evandrosouza-developer/ps2tomsxUSB/Documentation/Kicad/F4/PS2-MSX-F4 Back view.png

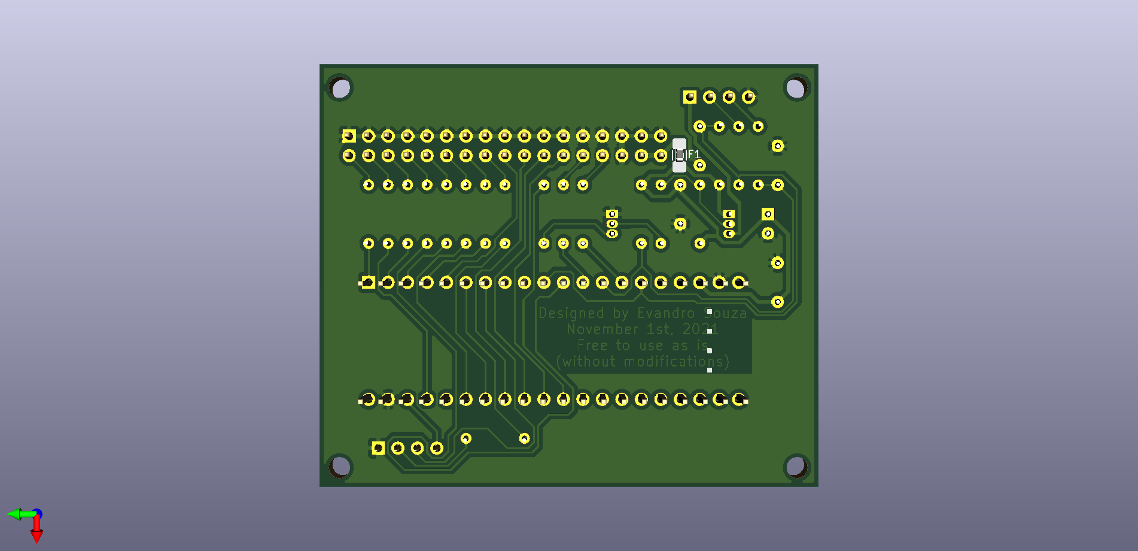
Documentation/Kicad/F4/PS2-MSX-F4 Back view.png
