evandrosouza-developer/ps2tomsxUSB/database.c

/** @addtogroup 05 dbasemgt Database Management
 *
 * @file database.c Database definition file input.
 *
 * @brief <b>Database definition, check and maintenance routines.</b>
 *
 * @version 1.0.0
 *
 * @author @htmlonly &copy; @endhtmlonly 2022
 * Evandro Souza <evandro.r.souza@gmail.com>
 *
 * @date 25 September 2022
 *
 * This library executes functions to interface and control a PS/2 keyboard, like:
 * power control of a PS/2 key, general interface to read events and write commands to PS/2
 * keyboard, including interrupt service routines on the STM32F4 and STM32F1 series of ARM
 * Cortex Microcontrollers by ST Microelectronics.
 *
 * LGPL License Terms ref lgpl_license
 */

/*
 * This file is part of the PS/2 to MSX Keyboard converter enviroment:
 * PS/2 to MSX keyboard Converter and MSX Keyboard Subsystem Emulator
 * designs, based on libopencm3 project.
 *
 * Copyright (C) 2022 Evandro Souza <evandro.r.souza@gmail.com>
 *
 * This original SW is compiled to a Sharp/Epcom MSX HB-8000 and a brazilian ABNT2 PS/2 keyboard (ID=275)
 * But it is possible to update the table sending a Intel Hex File through serial or USB
 *
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
 * You should have received a copy of the GNU Lesser General Public License
 * along with this library.  If not, see <http://www.gnu.org/licenses/>.
 */

//Use Tab width=2



const uint8_t 
#if MCU == STM32F103
__attribute__((section("MSXDATABASE"))) 
#endif  //#if MCU == STM32F103
DEFAULT_MSX_KEYB_DATABASE_CONVERSION[(uint16_t)N_DATABASE_REGISTERS][(uint8_t)DB_NUM_COLS] =
//Paste here the generated excel Conversion Database to make it as a default.
//Colar aqui Base de Dados de conversao gerada pelo excel para compilar como uma tabela default.
{
    {1, 0, 255, 255, 255, 255, 255, 255},
    {1, 0, 0, 244, 96, 112, 255, 255},
    {3, 0, 0, 244, 113, 255, 255, 255},
    {4, 0, 0, 244, 103, 255, 255, 255},
    {5, 0, 0, 244, 101, 255, 255, 255},
    {6, 0, 0, 244, 102, 255, 255, 255},
    {7, 0, 0, 244, 116, 255, 255, 255},
    {9, 0, 0, 244, 96, 113, 255, 255},
    {10, 0, 0, 244, 96, 103, 255, 255},
    {11, 0, 0, 244, 96, 101, 255, 255},
    {12, 0, 0, 244, 112, 255, 255, 255},
    {13, 0, 0, 244, 115, 255, 255, 255},
    {14, 0, 0, 246, 96, 22, 6, 255},
    {17, 0, 0, 244, 100, 255, 255, 255},
    {18, 0, 0, 244, 96, 255, 255, 255},
    {20, 0, 0, 244, 97, 255, 255, 255},
    {21, 0, 0, 244, 70, 255, 255, 255},
    {22, 0, 0, 244, 1, 255, 255, 255},
    {26, 0, 0, 244, 87, 255, 255, 255},
    {27, 0, 0, 244, 80, 255, 255, 255},
    {28, 0, 0, 244, 38, 255, 255, 255},
    {29, 0, 0, 244, 84, 255, 255, 255},
    {30, 0, 0, 244, 2, 255, 255, 255},
    {33, 0, 0, 244, 48, 255, 255, 255},
    {34, 0, 0, 244, 85, 255, 255, 255},
    {35, 0, 0, 244, 49, 255, 255, 255},
    {36, 0, 0, 244, 50, 255, 255, 255},
    {37, 0, 0, 244, 4, 255, 255, 255},
    {38, 0, 0, 244, 3, 255, 255, 255},
    {41, 0, 0, 244, 128, 255, 255, 255},
    {42, 0, 0, 244, 83, 255, 255, 255},
    {43, 0, 0, 244, 51, 255, 255, 255},
    {44, 0, 0, 244, 81, 255, 255, 255},
    {45, 0, 0, 244, 71, 255, 255, 255},
    {46, 0, 0, 244, 5, 255, 255, 255},
    {49, 0, 0, 244, 67, 255, 255, 255},
    {50, 0, 0, 244, 39, 255, 255, 255},
    {51, 0, 0, 244, 53, 255, 255, 255},
    {52, 0, 0, 244, 52, 255, 255, 255},
    {53, 0, 0, 244, 86, 255, 255, 255},
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
};
